mluckham54/dc42MetalDetector/MetalDetector/Photos/20250127_202558.jpg

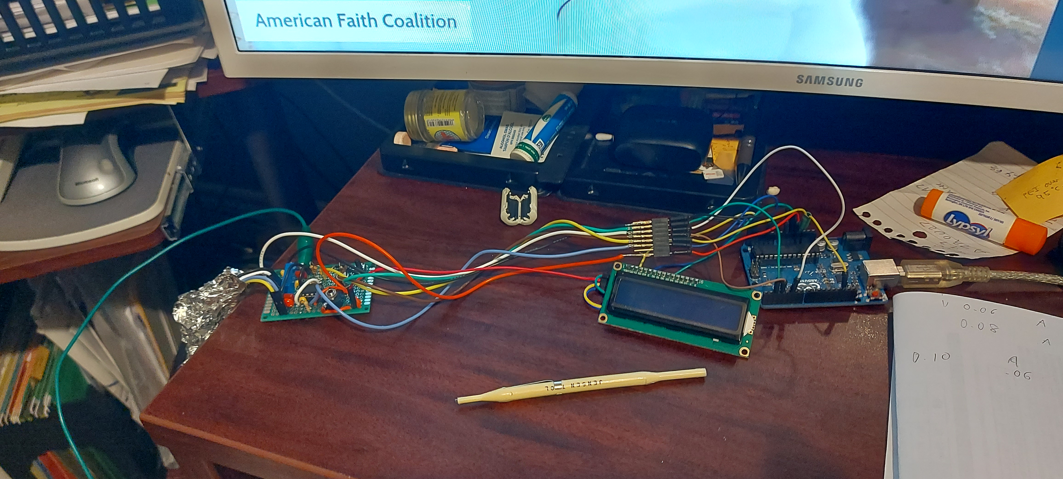
MetalDetector/Photos/20250127_202558.jpg
