mluckham54/dc42MetalDetector/MetalDetector/Photos/20250129_143607.jpg

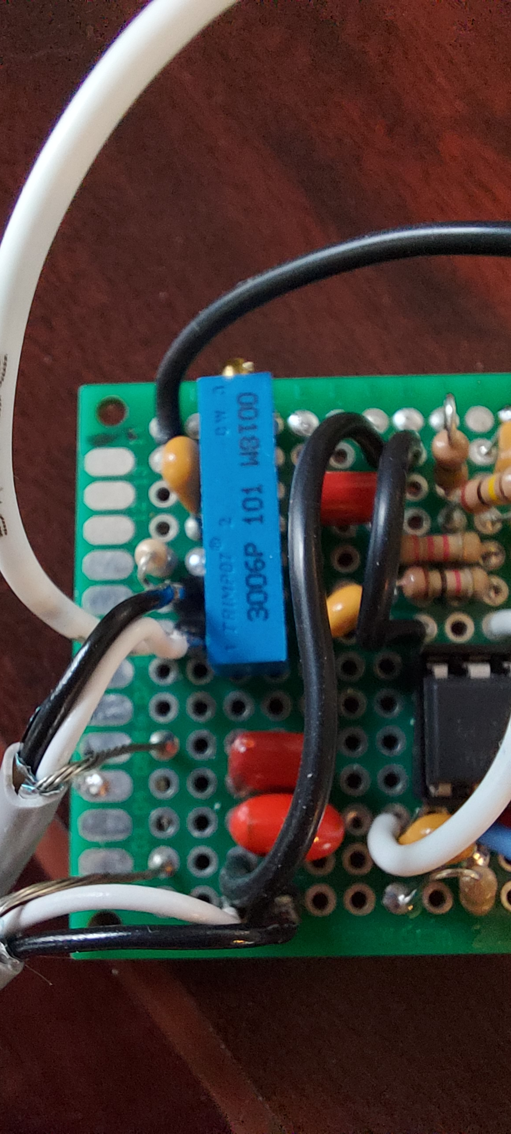
MetalDetector/Photos/20250129_143607.jpg
