mluckham54/dc42MetalDetector/MetalDetector/Photos/20250206_145954.jpg

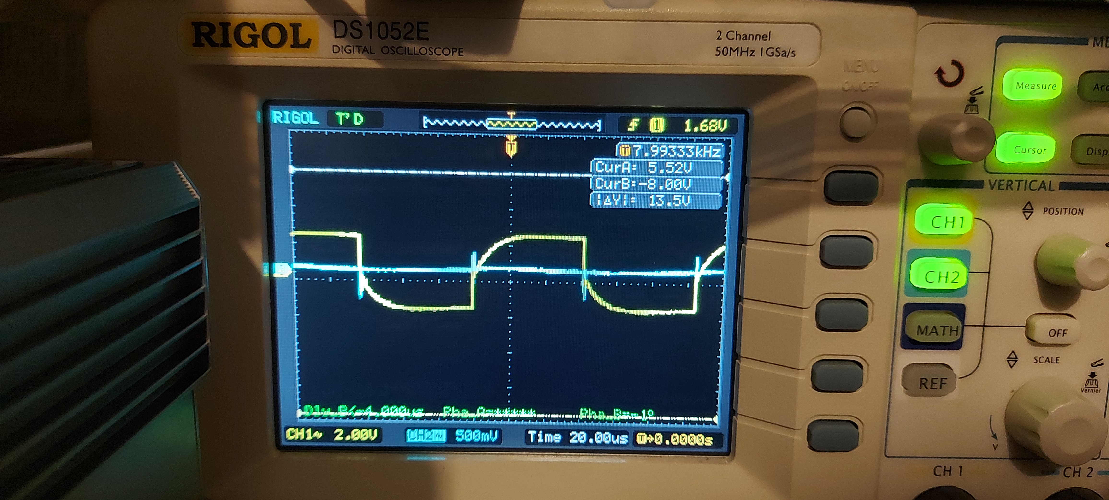
MetalDetector/Photos/20250206_145954.jpg
