mluckham54/dc42MetalDetector/MetalDetector/Photos/20250206_150053.jpg

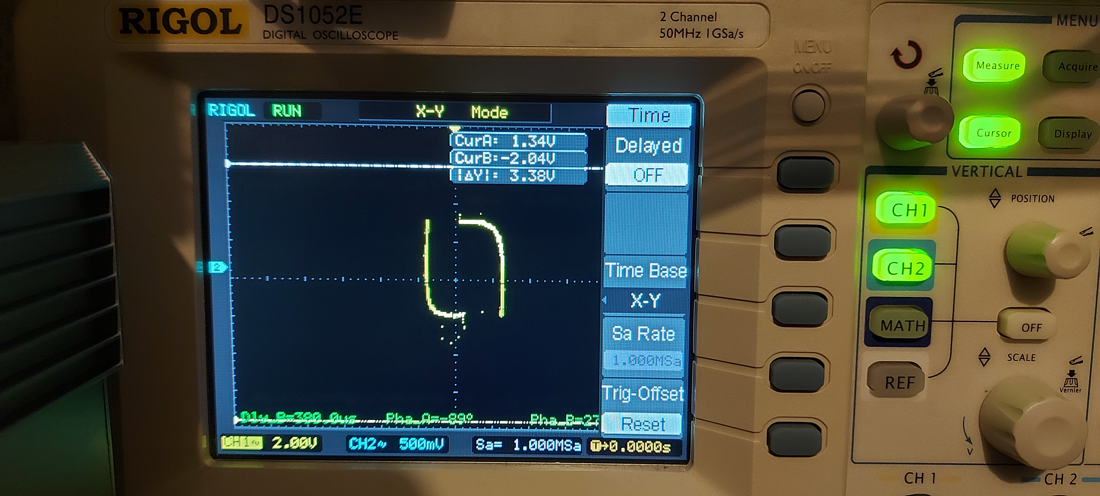
MetalDetector/Photos/20250206_150053.jpg
