mluckham54/dc42MetalDetector/MetalDetector/Photos/20250206_150109.jpg

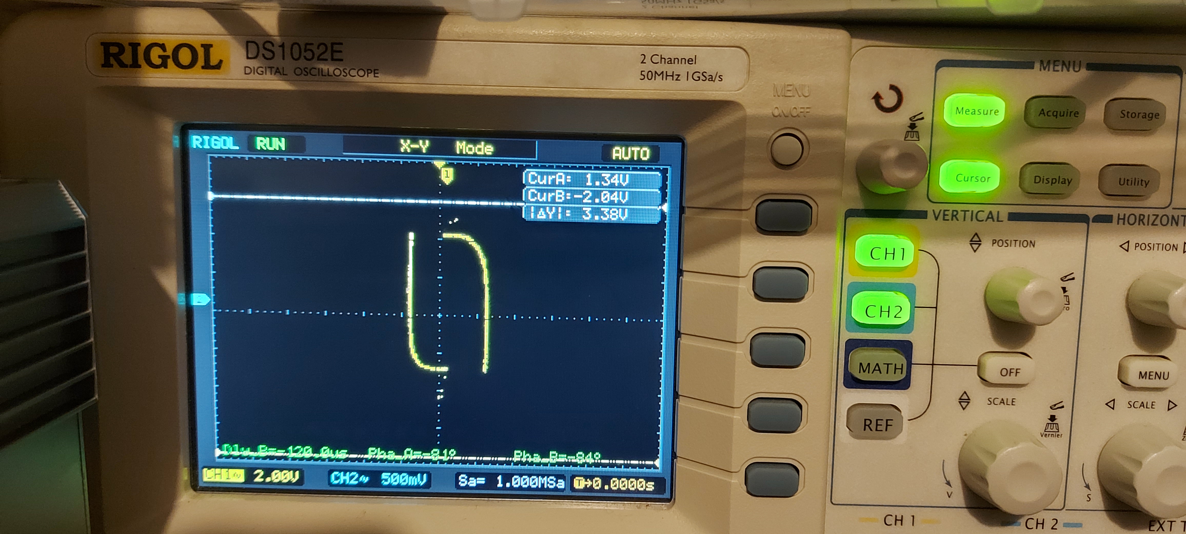
MetalDetector/Photos/20250206_150109.jpg
