mluckham54/dc42MetalDetector/MetalDetector/Photos/20250206_150717.jpg

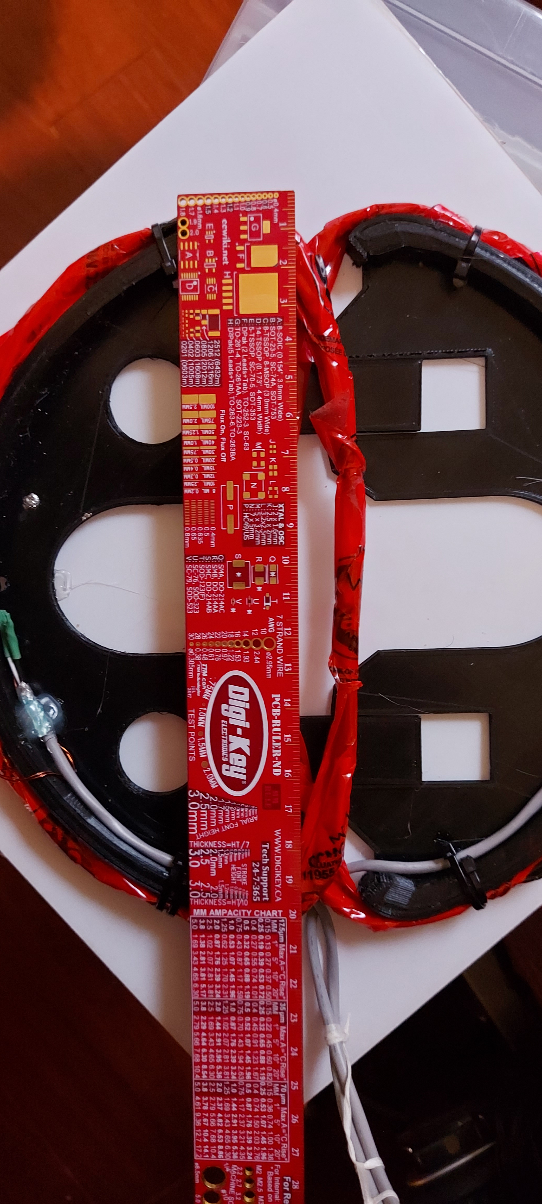
MetalDetector/Photos/20250206_150717.jpg
