mluckham54/dc42MetalDetector/MetalDetector/PrintableParts/DD Coil modifiable - 5966085 - 105percent/images/9db437f4-f30a-43c5-86a0-b26be82b5d1f.jpeg

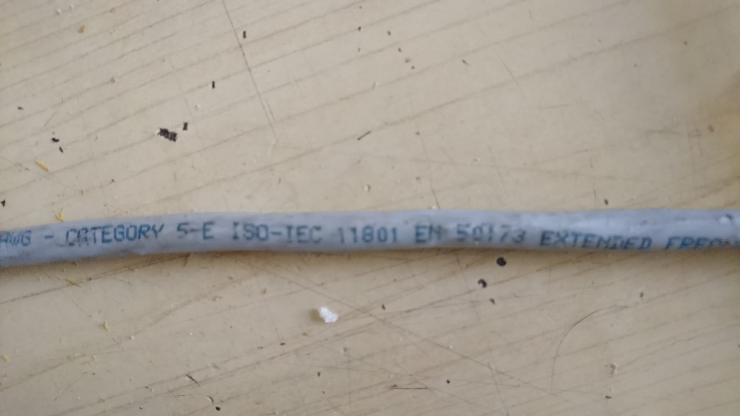
MetalDetector/PrintableParts/DD Coil modifiable - 5966085 - 105percent/images/9db437f4-f30a-43c5-86a0-b26be82b5d1f.jpeg
