mluckham54/dc42MetalDetector/MetalDetector/PrintableParts/DD Coil modifiable - 5966085 - 105percent/images/67e6f32b-952f-4510-a782-5e5aab1b4258.jpeg

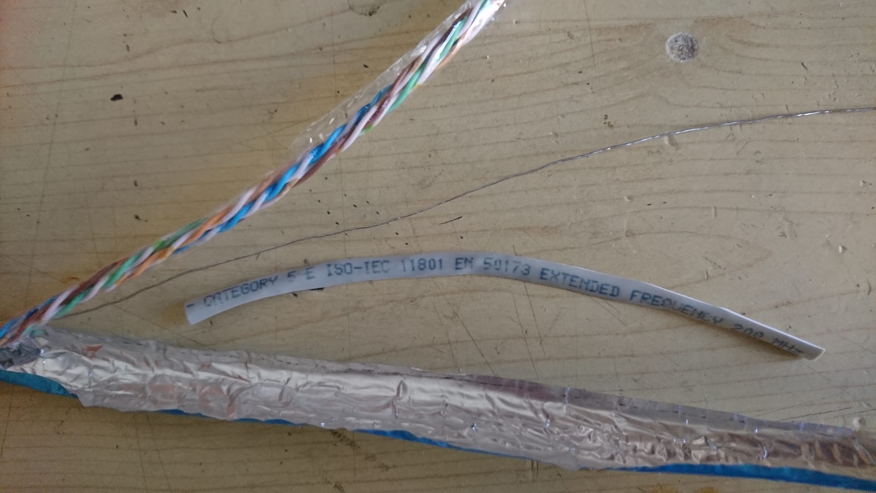
MetalDetector/PrintableParts/DD Coil modifiable - 5966085 - 105percent/images/67e6f32b-952f-4510-a782-5e5aab1b4258.jpeg
