mluckham54/dc42MetalDetector/MetalDetector/PrintableParts/DD Coil modifiable - 5966085 - 105percent/images/94d3f9c3-4655-4cd1-a8c8-2395922d033d.jpeg

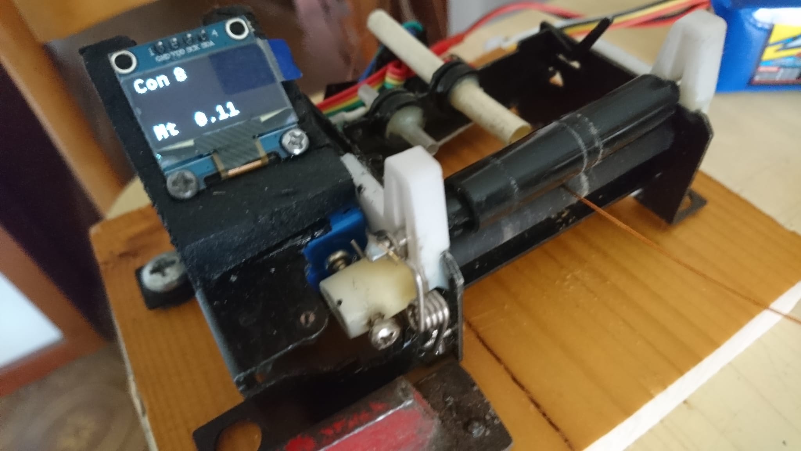
MetalDetector/PrintableParts/DD Coil modifiable - 5966085 - 105percent/images/94d3f9c3-4655-4cd1-a8c8-2395922d033d.jpeg
