mluckham54/dc42MetalDetector/MetalDetector/PrintableParts/DD Coil modifiable - 5966085 - 105percent/images/a807b9a6-012e-4c42-b0f4-f7ac6dd4b872.jpeg

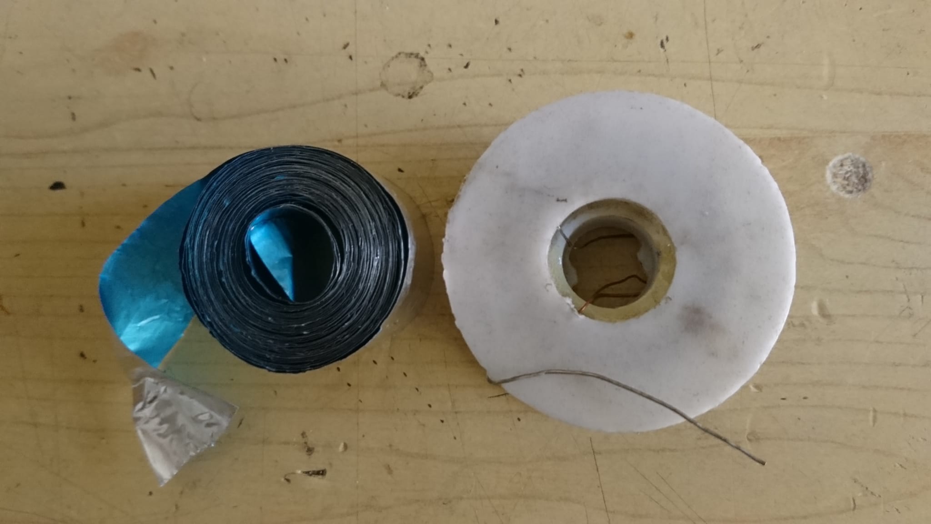
MetalDetector/PrintableParts/DD Coil modifiable - 5966085 - 105percent/images/a807b9a6-012e-4c42-b0f4-f7ac6dd4b872.jpeg
