mluckham54/dc42MetalDetector/MetalDetector/PrintableParts/DD Coil modifiable - 5966085 - 105percent/images/bcf26d11-5bbe-42b0-b15c-80d85e8d5795.jpeg

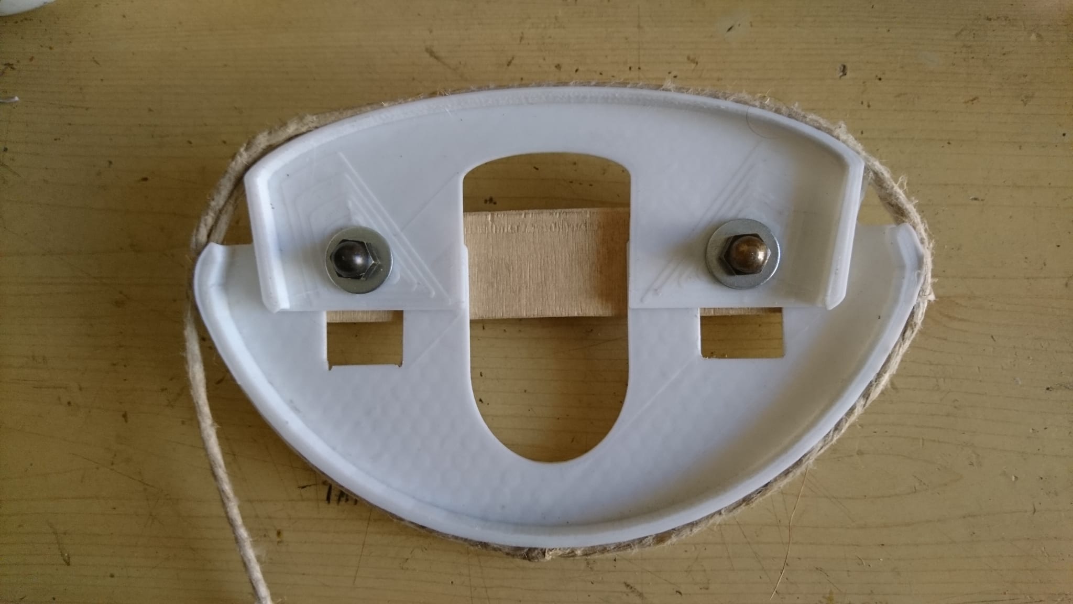
MetalDetector/PrintableParts/DD Coil modifiable - 5966085 - 105percent/images/bcf26d11-5bbe-42b0-b15c-80d85e8d5795.jpeg
