mluckham54/dc42MetalDetector/MetalDetector/Photos/20250206_150626.jpg

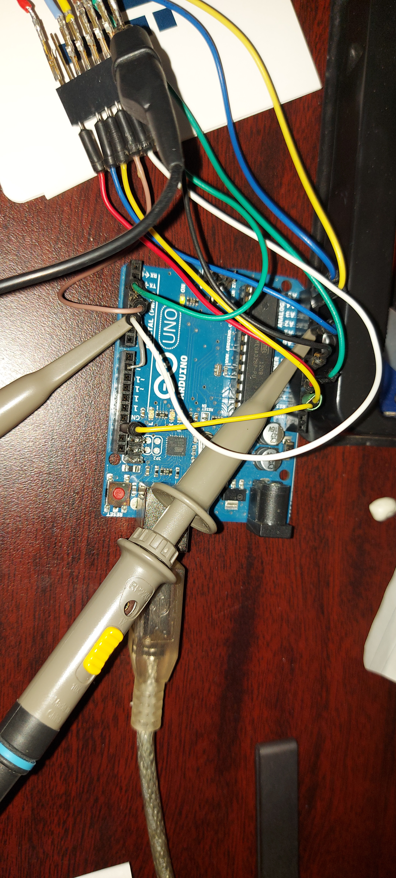
MetalDetector/Photos/20250206_150626.jpg
